Hack-a-Day/Vectorscope/inspiration/DSC_0219_thumbnail.png

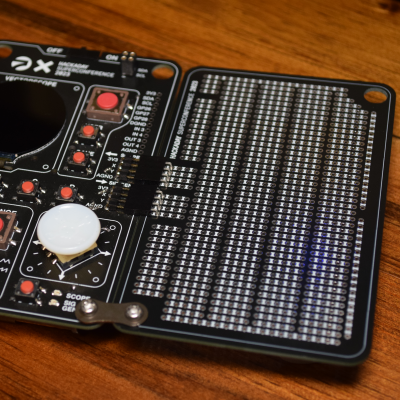
inspiration/DSC_0219_thumbnail.png
