Hack-a-Day/Vectorscope/inspiration/tek515afront.jpg

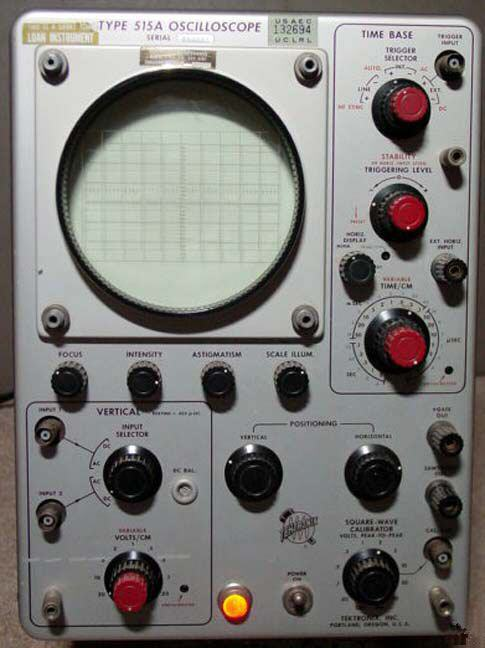
inspiration/tek515afront.jpg
