Hack-a-Day/Vectorscope/source/pl_earth.jpg

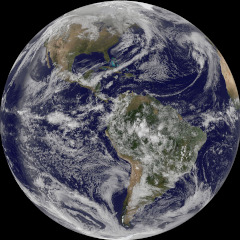
source/pl_earth.jpg
