Hack-a-Day/Vectorscope/source/pl_jupiter.jpg

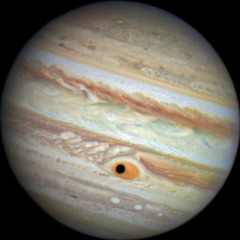
source/pl_jupiter.jpg
