Hack-a-Day/Vectorscope/source/pl_mars.jpg

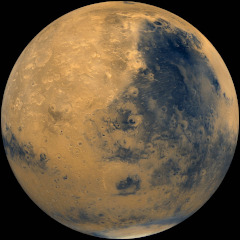
source/pl_mars.jpg
