Hack-a-Day/Vectorscope/source/pl_mercury.jpg

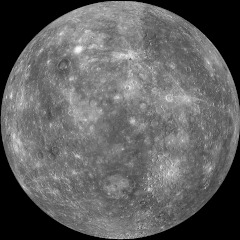
source/pl_mercury.jpg
