Hack-a-Day/Vectorscope/source/pl_pluto.jpg

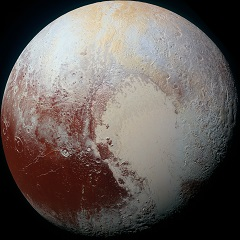
source/pl_pluto.jpg
