Hack-a-Day/Vectorscope/source/pl_saturn.jpg

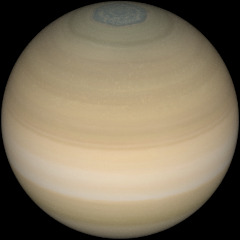
source/pl_saturn.jpg
