Hack-a-Day/Vectorscope/source/pl_thats_no_moon.jpg

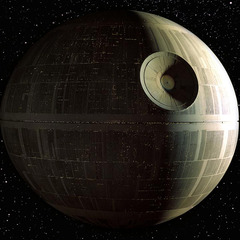
source/pl_thats_no_moon.jpg
