Hack-a-Day/Vectorscope/source/pl_uranus.jpg

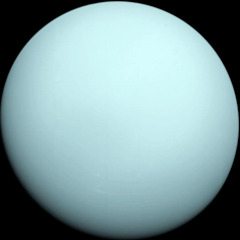
source/pl_uranus.jpg
