Hack-a-Day/Vectorscope/source/main.py

import _thread
import vectoros
from time import sleep

import machine
user_button = machine.Pin(19, machine.Pin.IN)
if user_button.value():
    vectoros.run()
else:
    import vectorscope
    v = vectorscope.Vectorscope()
